mikeysklar/hil-hub-port-authority/test-scripts/controller/code.py

# Port Authority I2C controller, idle sketch.
# Does nothing on its own so the hub tests drive everything from the REPL.
# Deliberately touches no SD/SDIO, no I2C, no pins.
print("port authority controller idle")
